Noahnc/Projektarbeit_Mikrocomputer/ESP8266_Sensor/include/Sensor_Handler.h

#ifndef Sensor_Handler_h
#define Sensor_Handler_h

#include <SPI.h>
#include <Adafruit_Sensor.h>
#include "Adafruit_BME680.h"
#include <Wire.h>
#include <iostream>

class Sensor_Handler
{
private:
#define SEALEVELPRESSURE_HPA (1013.25)
    Adafruit_BME680 bme;
    String Temparature;
    String Presure;
    String Humidity;
    String Gas;
    String Altitude;

public:
    void init();
    bool readSensorData();
    float getTemp();
    float getPresure();
    float getHumidity();
    float getGas();
    float getAltitude();
};

#endif
