Noahnc/Projektarbeit_Mikrocomputer/ESP8266_Sensor/include/00config.h

/*
########################################################################
#                  Globale konfigurations variablen
########################################################################
#                           Description
#            In dieser Datei sind alle globalen Variablen
*/

#pragma once

namespace config_constants
{
    // Stationsname, muss gleich sein wie Name in SQL DB:
    const String ESP_Hostname = "ESP-Projektarbeit-Mikrocomputer";

    // WiFi Config:
    const String wifi_ssid = "Demo";
    const String wifi_wpa_psk = "Demo2021735bd";

    // NTP Server:
    const String NTP_Server = "ch.pool.ntp.org";

    // MQTT Server angaben:
    const String mosquitto_server = "projektarbeit-mikrocomputer.canadea.ch";
    const String mosquitto_user = "mqtt_user";
    const String mosquitto_pw = "jfjhHbhf86edjdjHG";

    // Debug Mode (gibt diverse Informationen per Serial aus)
    const bool debug_mode = false;

    // Intervall in Sekunden, in welchem Daten ausgewertet und per mqtt übermittelt werden.
    const int mqtt_update_interval = 30;

    // RGB LED pins
    static const int led_red = 15;
    static const int led_green = 13;
    static const int led_blue = 12;

    const char mosquitto_ca[] PROGMEM = R"EOF(
-----BEGIN CERTIFICATE-----
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
6MhpQSE=
-----END CERTIFICATE-----
)EOF";

    const char mosquitto_pub_key[] PROGMEM = R"KEY(
-----BEGIN PUBLIC KEY-----
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
OwIDAQAB
-----END PUBLIC KEY-----
)KEY";

}
