Noahnc/Projektarbeit_Mikrocomputer/ESP8266_Sensor/include/MQTT_Handler.h

#ifndef MQTT_Handler_h
#define MQTT_Handler_h

#include <PubSubClient.h>
#include <iostream>
#include <ESP8266WiFi.h>
#include "RGB_LED_Handler.h"
#include <string>
#include <Arduino.h>
#include <00config.h>

class MQTT_Handler

{


private:
    String MQTT_Server;
    String MQTT_User;
    String MQTT_Pw;
    const char *Server;
    BearSSL::WiFiClientSecure espClient;
    PubSubClient client;
    String clientId;
    BearSSL::X509List cert;
    BearSSL::PublicKey publicKey;

public:
    static RGB_LED_Handler LED;
    MQTT_Handler(String server, String user, String pw, String id);
    void init();
    void reconnect();
    bool CheckConnection();
    void SendData(char const *topic, String Data);
    static void callback(char *topic, byte *message, unsigned int length);
    void ReadIncoming();
};

#endif
