Noahnc/Projektarbeit_Mikrocomputer/ESP8266_Sensor/src/WiFi_Handler.cpp

/*
########################################################################
#                           WiFi Handler
########################################################################
#                           Description
#   Handelt das den WLAN Verbindungsaufbau und dessen Zustand
*/

#include <ESP8266WiFi.h>
#include "WiFi_Handler.h"
#include <Arduino.h>
#include "00config.h"
#include <string>
#include <IPAddress.h>


using namespace config_constants;

WiFi_Handler::WiFi_Handler(String ssid, String pw, String hostname)
{
    SSID = ssid;
    Password = pw;
    Hostname = hostname;
}

void WiFi_Handler::init()
{
    if (debug_mode)
    {
        Serial.println();
        Serial.print("Connecting to SSID: " + SSID);
    }
    WiFi.begin(SSID, Password);
    WiFi.setAutoConnect(true);
    WiFi.persistent(true);
    WiFi.setHostname(Hostname.c_str());

    while (WiFi.status() != WL_CONNECTED)
    {
        if (debug_mode)
        {
            Serial.print(".");
        }
        delay(50);
    }
    if (debug_mode)
    {
        Serial.println("");
        Serial.println("SSID " + SSID + " connected");
    }

}
String WiFi_Handler::getNetworkiP()
{
    IPAddress ip = WiFi.localIP();
    String s = "";
    for (int i = 0; i < 4; i++)
        s += i ? "." + String(ip[i]) : String(ip[i]);
    return s;
}

bool WiFi_Handler::CheckWiFiConnected()
{
    if (WiFi.status() == WL_CONNECTED)
    {
        return true;
    }
    else
    {
        return false;
    }
}

String WiFi_Handler::getConnectedSSID()
{
    return SSID;
}

int WiFi_Handler::getWiFiRSSI()
{

    return WiFi.RSSI();
}

String WiFi_Handler::getHostname()
{
    return WiFi.hostname();
}
